JochiPochi/LazIRTag/KiCad/Player-Health/Player-Health.sch

## KiCad design KiCad/Player-Health/Player-Health.sch (2016-04-13)

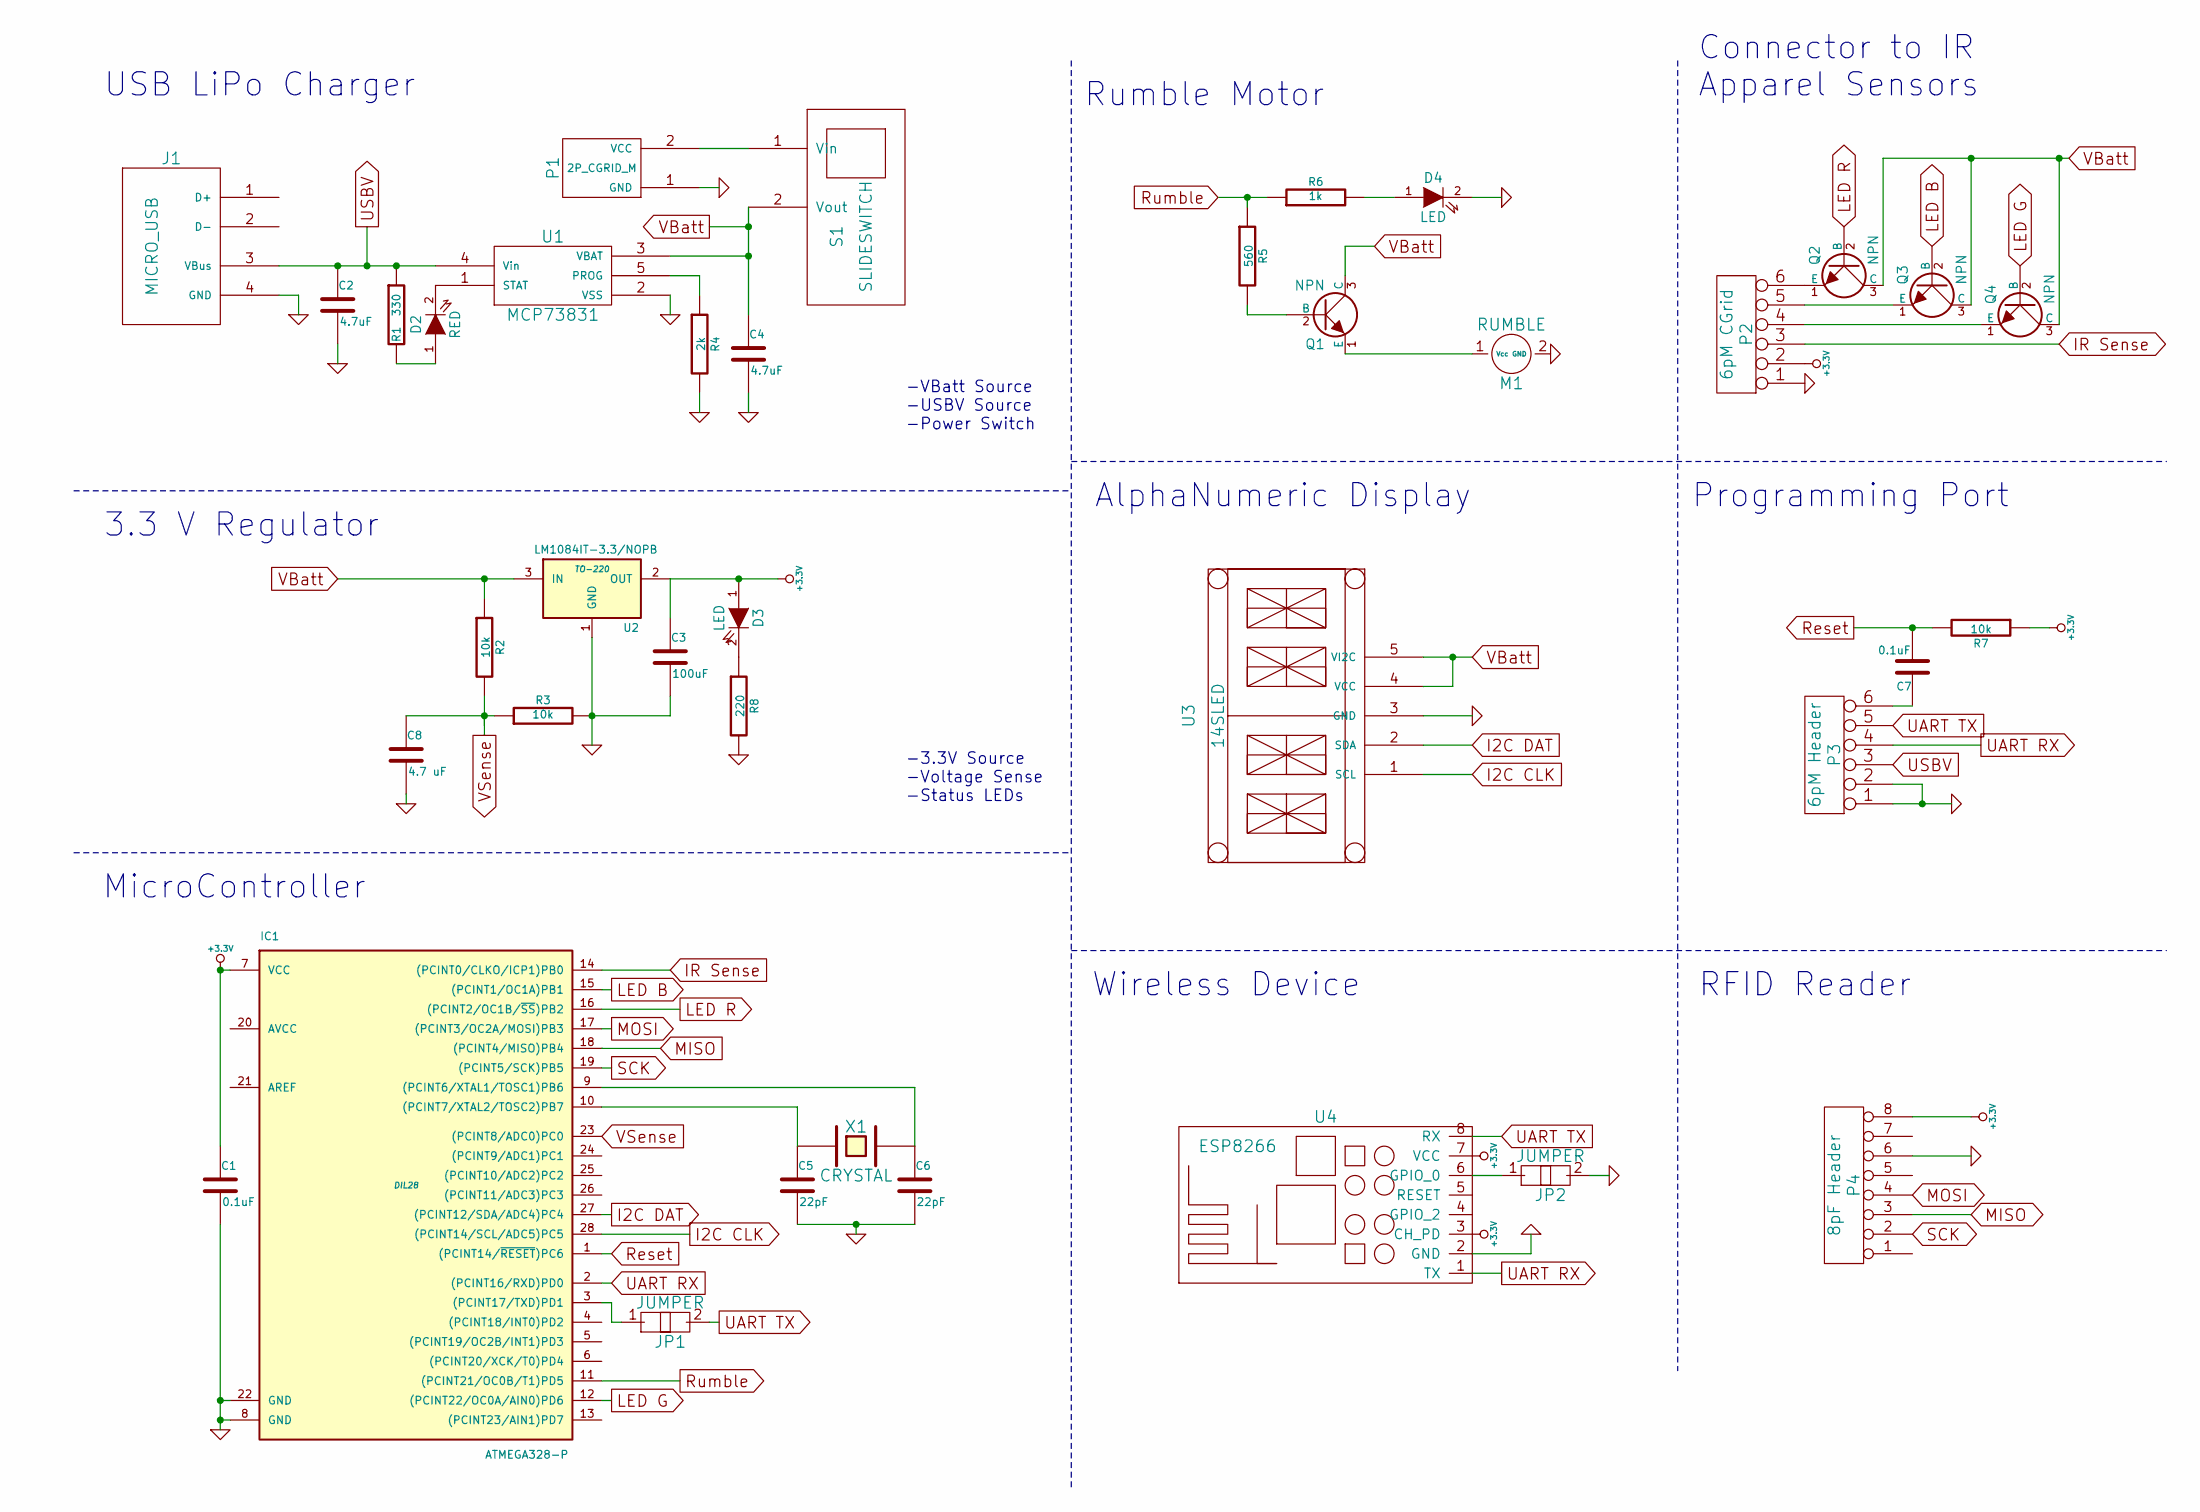
[picture p9: schematic Player-Health.sch]

Parts:
C1, C7: 0.1uF
C2, C4: 4.7uF
C3: 100uF
C5, C6: 22pF
C8: 4.7 uF
D2: RED
D3, D4: LED
IC1: ATMEGA328-P; DIL28
J1: MICRO_USB
JP1: JUMPER
JP2: JUMPER
M1: RUMBLE
P1: 2P_CGRID_M
P2: 6pM CGrid
P3: 6pM Header
P4: 8pF Header
Q1, Q2, Q3, Q4: NPN
R1: 330
R2, R3, R7: 10k
R4: 2k
R5: 560
R6: 1k
R8: 220
S1: SLIDESWITCH
U1: MCP73831
U2: LM1084IT-3.3/NOPB; TO-220
U3: 14SLED
U4: ESP8266
X1: CRYSTAL

Connections:
+3.3V: C1.1, C3.1, D3.1 (A), IC1.7 (VCC), P2.2, P4.8, R7.1, U2.2 (OUT), U4.3 (CH_PD), U4.7 (VCC)
GND: C1.2, C2.2, C3.2, C4.2, C5.2, C6.2, C8.2, D4.2 (K), IC1.8 (GND), IC1.22 (GND), J1.4 (GND), JP2.2, M1.2 (GND), P1.1 (GND), P2.1, P3.1, P3.2, P4.6, R3.2, R4.2, R8.2, U1.2 (VSS), U2.1 (GND), U3.3 (GND), U4.2 (GND)
I2C CLK: IC1.28 ((PCINT14/SCL/ADC5)PC5), U3.1 (SCL)
I2C DAT: IC1.27 ((PCINT12/SDA/ADC4)PC4), U3.2 (SDA)
IR Sense: IC1.14 ((PCINT0/CLKO/ICP1)PB0), P2.3
LED B: IC1.15 ((PCINT1/OC1A)PB1), Q3.2 (B)
LED G: IC1.12 ((PCINT22/OC0A/AIN0)PD6), Q4.2 (B)
LED R: IC1.16 ((PCINT2/OC1B/~SS~)PB2), Q2.2 (B)
MISO: IC1.18 ((PCINT4/MISO)PB4), P4.3
MOSI: IC1.17 ((PCINT3/OC2A/MOSI)PB3), P4.4
unnamed: C5.1, IC1.10 ((PCINT7/XTAL2/TOSC2)PB7), X1.1
unnamed: C6.1, IC1.9 ((PCINT6/XTAL1/TOSC1)PB6), X1.2
unnamed: C7.1, P3.6
unnamed: D2.1 (A), R1.2
unnamed: D2.2 (K), U1.1 (STAT)
unnamed: D3.2 (K), R8.1
unnamed: D4.1 (A), R6.2
unnamed: IC1.3 ((PCINT17/TXD)PD1), JP1.1
unnamed: JP2.1, U4.6 (GPIO_0)
unnamed: M1.1 (Vcc), Q1.1 (E)
unnamed: P1.2 (VCC), S1.1 (Vin)
unnamed: P2.4, Q4.1 (E)
unnamed: P2.5, Q3.1 (E)
unnamed: P2.6, Q2.1 (E)
unnamed: Q1.2 (B), R5.2
unnamed: R4.1, U1.5 (PROG)
Reset: C7.2, IC1.1 ((PCINT14/~RESET~)PC6), R7.2
Rumble: IC1.11 ((PCINT21/OC0B/T1)PD5), R5.1, R6.1
SCK: IC1.19 ((PCINT5/SCK)PB5), P4.2
UART RX: IC1.2 ((PCINT16/RXD)PD0), P3.4, U4.1 (TX)
UART TX: JP1.2, P3.5, U4.8 (RX)
USBV: C2.1, J1.3 (VBus), P3.3, R1.1, U1.4 (Vin)
VBatt: C4.1, Q1.3 (C), Q2.3 (C), Q3.3 (C), Q4.3 (C), R2.1, S1.2 (Vout), U1.3 (VBAT), U2.3 (IN), U3.4 (VCC), U3.5 (VI2C)
VSense: C8.1, IC1.23 ((PCINT8/ADC0)PC0), R2.2, R3.1

Notes on the sheet:
USB LiPo Charger
-VBatt Source -USBV Source -Power Switch
3.3 V Regulator
-3.3V Source -Voltage Sense -Status LEDs
AlphaNumeric Display
MicroController
Wireless Device
Connector to IR Apparel Sensors
Programming Port
RFID Reader
Rumble Motor
