JochiPochi/LazIRTag/KiCad/Wrist Display Unit/Wrist Display Unit.sch

## KiCad design KiCad/Wrist Display Unit/Wrist Display Unit.sch (2016-04-13)

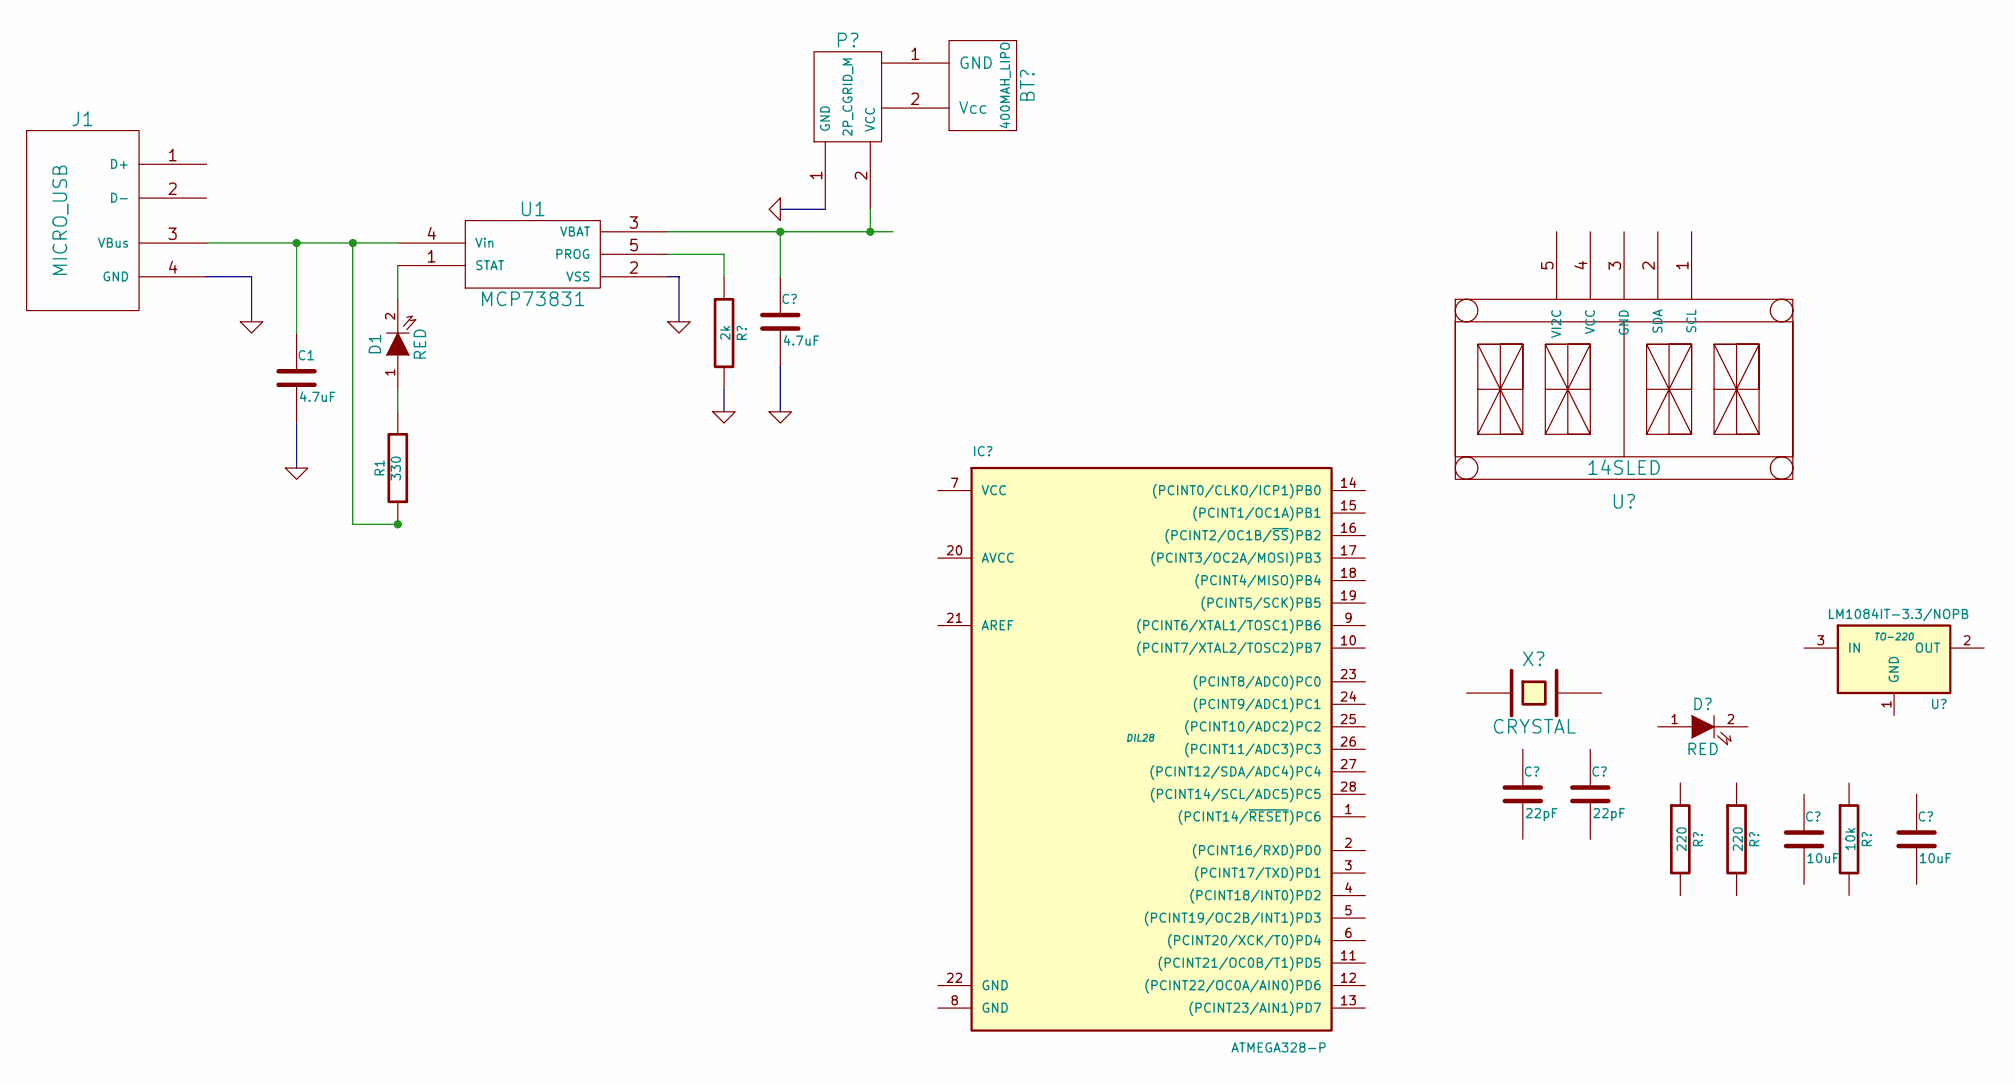
[picture p10: schematic Wrist Display Unit.sch]

Parts:
C1: 4.7uF
D1: RED
J1: MICRO_USB
R1: 330
U1: MCP73831

Connections:
unnamed: C1.1, J1.3 (VBus), R1.1, U1.4 (Vin)
unnamed: D1.1 (A), R1.2
unnamed: D1.2 (K), U1.1 (STAT)
